ductsoup/Feather-RTC/images/IMG_3888.JPG

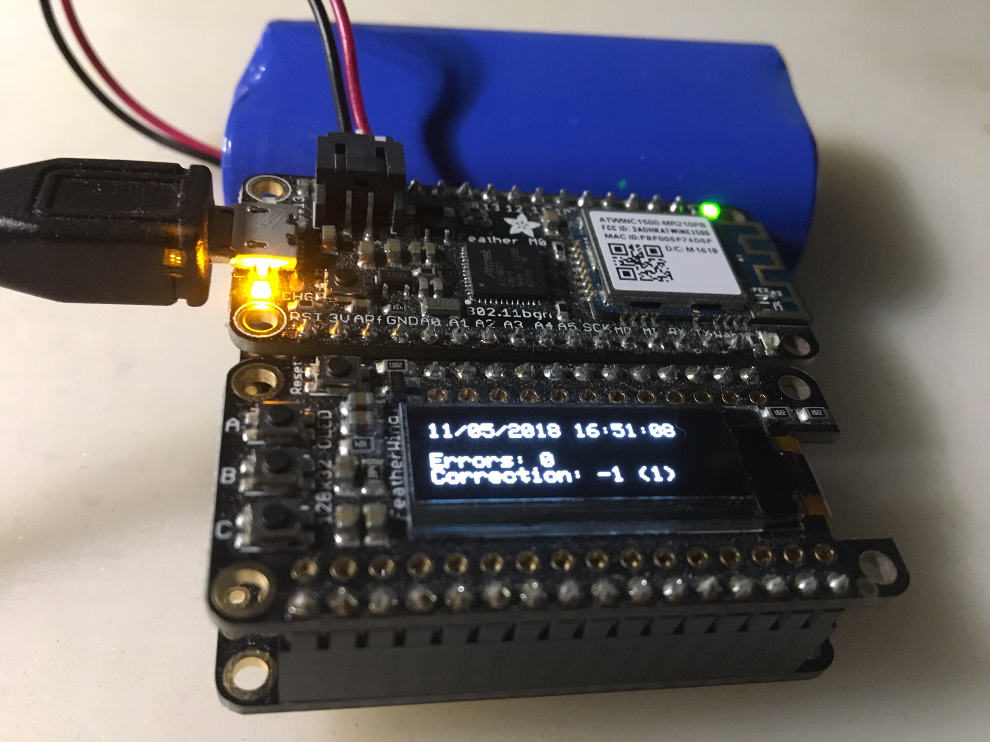
images/IMG_3888.JPG
