ductsoup/Feather-RTC/images/IMG_3891.JPG

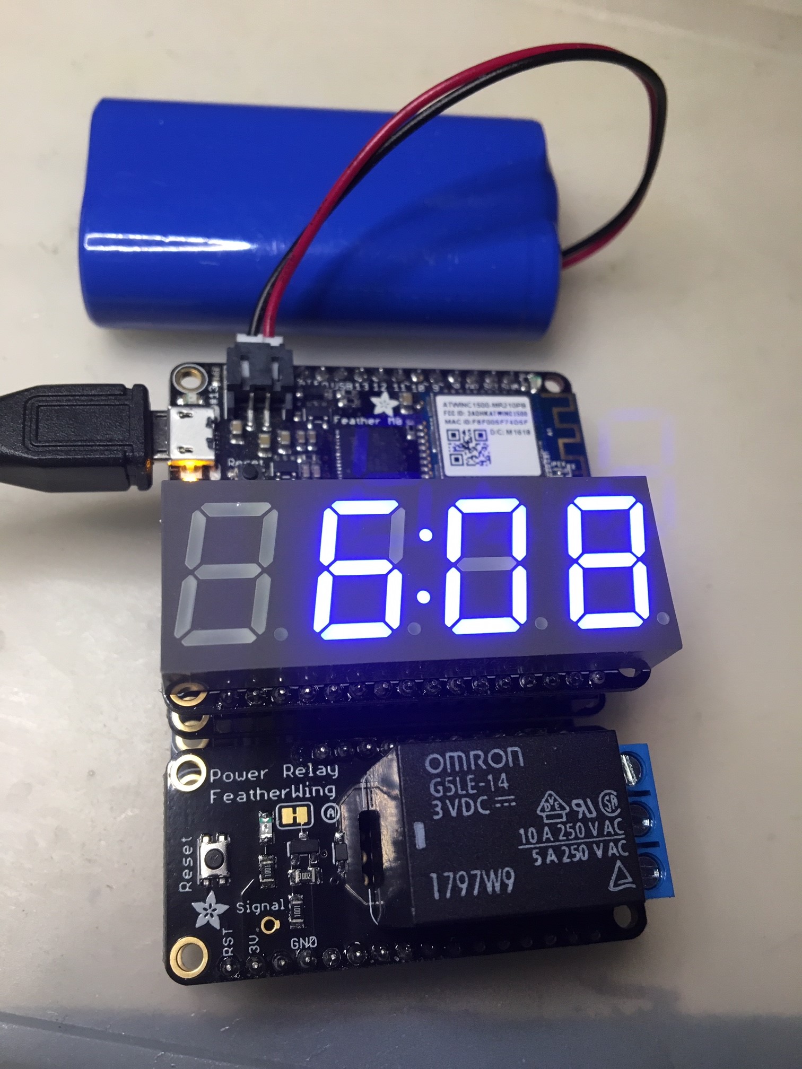
images/IMG_3891.JPG
