ductsoup/Feather-RTC/images/IMG_3924.JPG

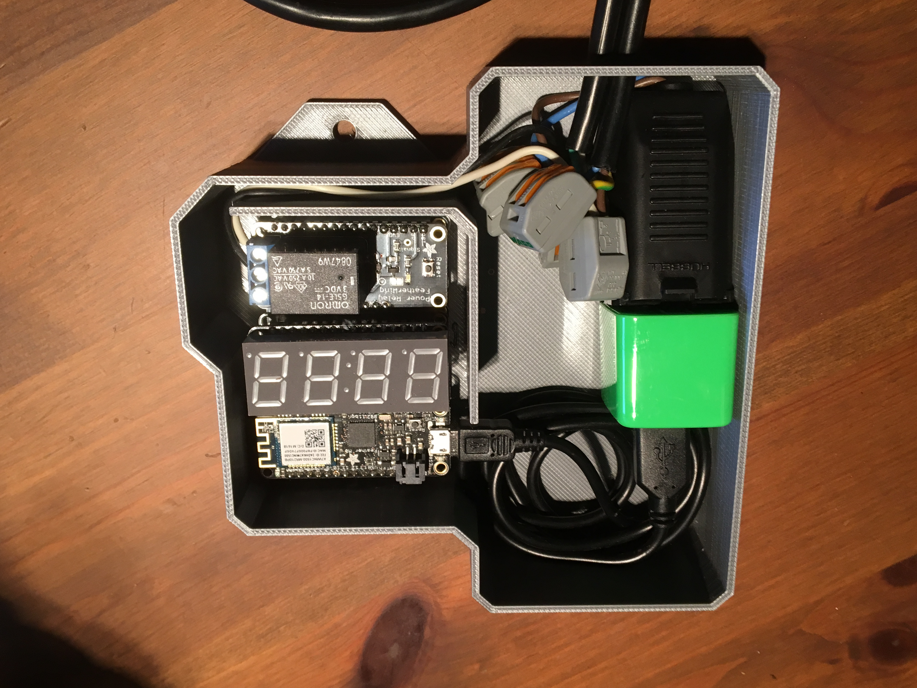
images/IMG_3924.JPG
